james-dire-1/arduino-radio-project/R_images/IMG_2889.jpeg

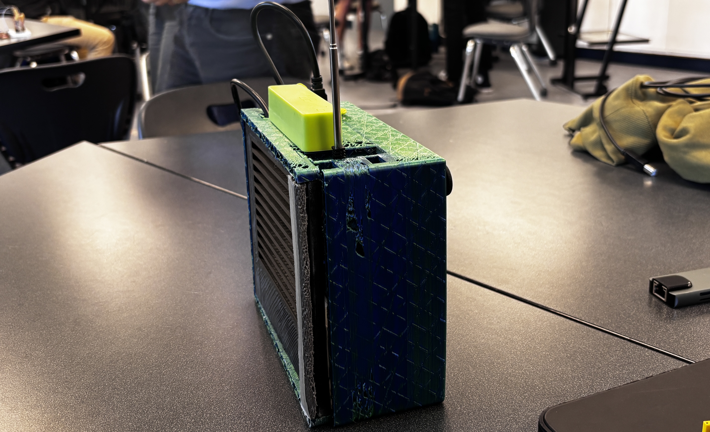
R_images/IMG_2889.jpeg
