james-dire-1/arduino-radio-project/R_images/IMG_2890.jpeg

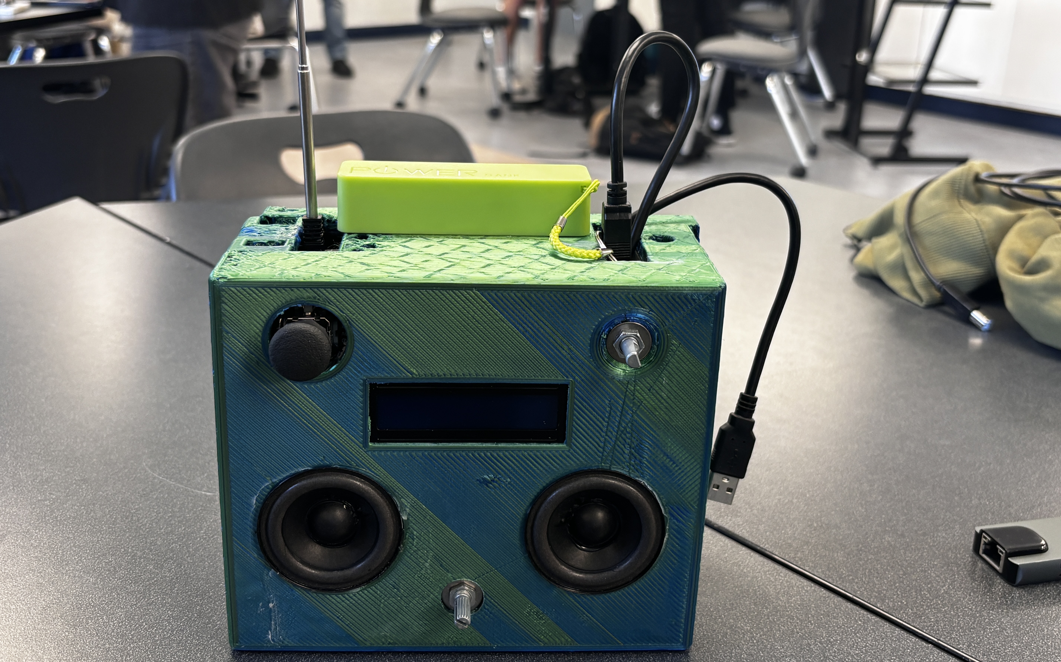
R_images/IMG_2890.jpeg
