james-dire-1/arduino-radio-project/R_other/CircuitDiagramImages/Screenshot 2025-05-31 at 1.21.56 PM.png

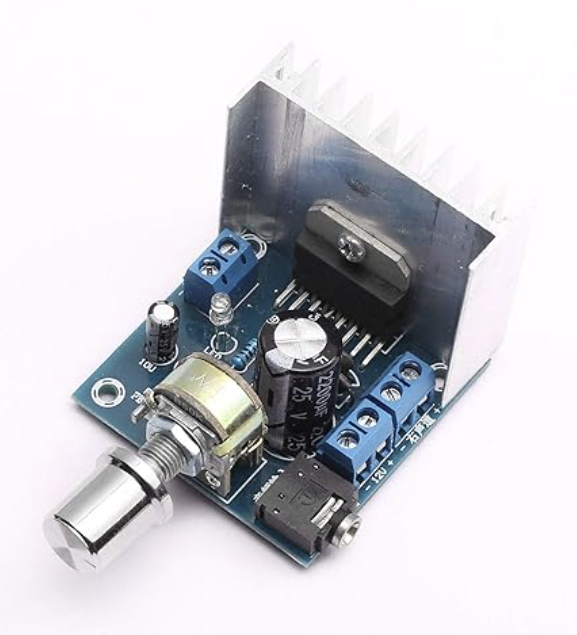
R_other/CircuitDiagramImages/Screenshot 2025-05-31 at 1.21.56 PM.png
