james-dire-1/arduino-radio-project/R_other/CircuitDiagramImages/TEA5767_fm_radio_module.webp

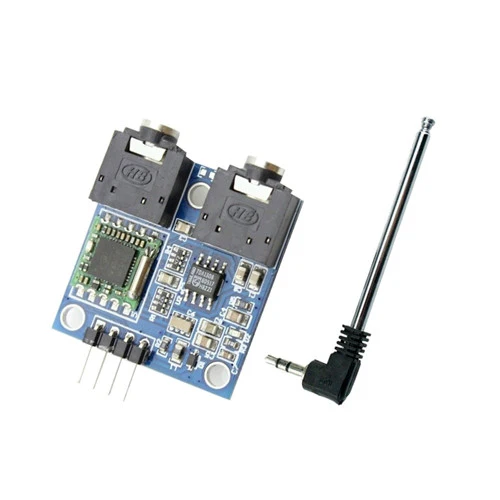
R_other/CircuitDiagramImages/TEA5767_fm_radio_module.webp
