james-dire-1/arduino-radio-project/R_other/SlideshowImages/6c5313c7-2e61-486a-ad82-d5e051c6e02a.png

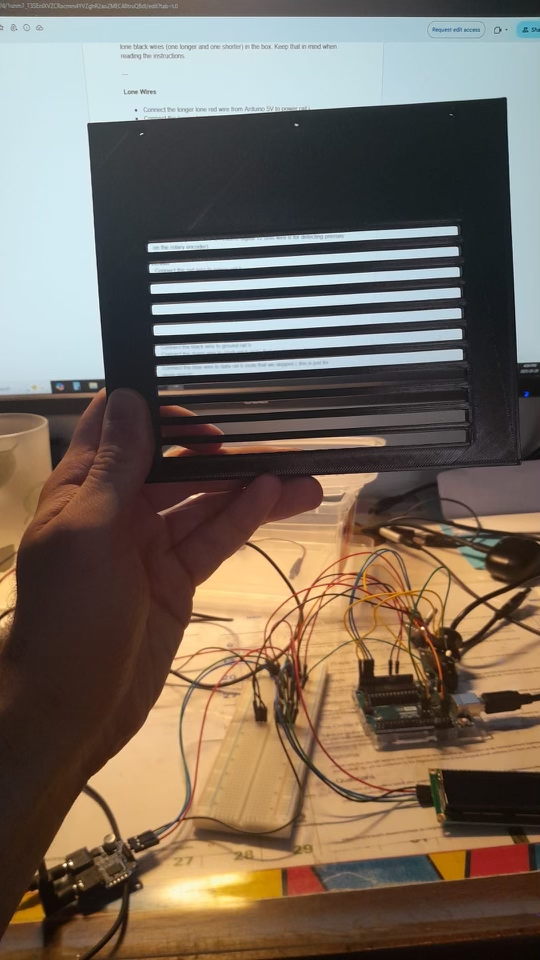
R_other/SlideshowImages/6c5313c7-2e61-486a-ad82-d5e051c6e02a.png
