james-dire-1/arduino-radio-project/R_other/SlideshowImages/7ecfe39c-ecb8-46d4-9817-e5481a1effc0.png

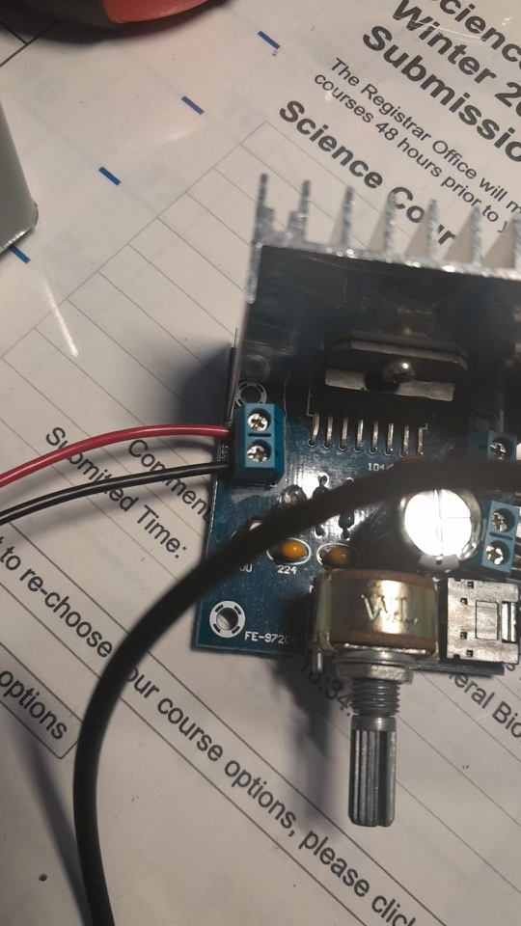
R_other/SlideshowImages/7ecfe39c-ecb8-46d4-9817-e5481a1effc0.png
