james-dire-1/arduino-radio-project/R_other/SlideshowImages/62ca493e-6e24-47a5-971f-845fc1b9c889.png

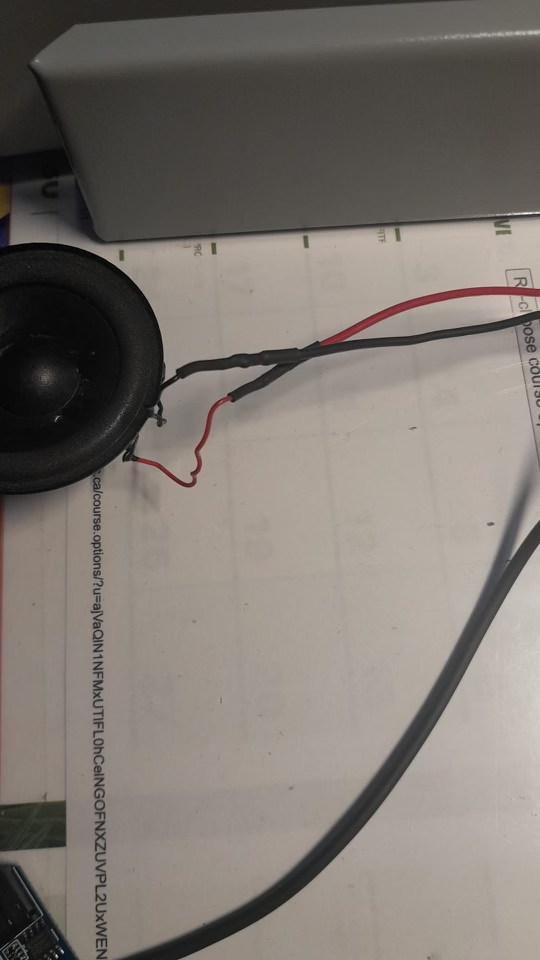
R_other/SlideshowImages/62ca493e-6e24-47a5-971f-845fc1b9c889.png
