james-dire-1/arduino-radio-project/R_other/SlideshowImages/95d62d8a-2fb8-4f7a-9237-26453b7603f2.png

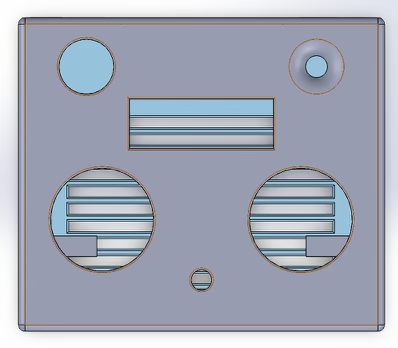
R_other/SlideshowImages/95d62d8a-2fb8-4f7a-9237-26453b7603f2.png
