james-dire-1/arduino-radio-project/R_other/SlideshowImages/ca7dd065-f66f-4d62-96de-7c329f59c99d.png

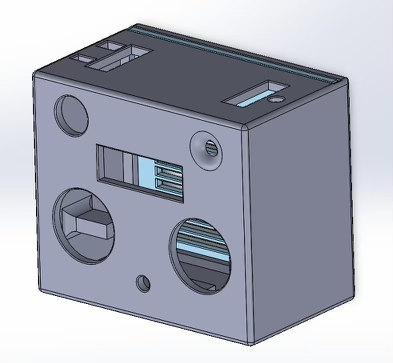
R_other/SlideshowImages/ca7dd065-f66f-4d62-96de-7c329f59c99d.png
