james-dire-1/arduino-radio-project/R_other/SlideshowImages/cb82eedb-ceaf-4a4e-8e40-77120ef748f7.png

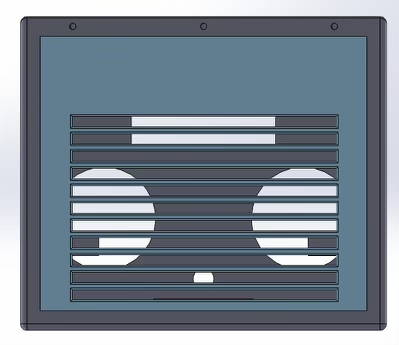
R_other/SlideshowImages/cb82eedb-ceaf-4a4e-8e40-77120ef748f7.png
