james-dire-1/arduino-radio-project/R_other/SlideshowImages/e50d46db-6967-4ef9-a702-23a1209742e0.png

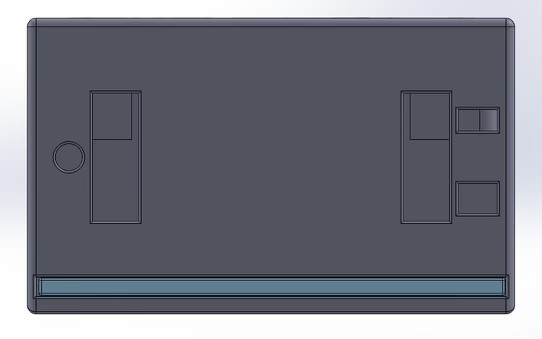
R_other/SlideshowImages/e50d46db-6967-4ef9-a702-23a1209742e0.png
