james-dire-1/arduino-radio-project/R_other/SlideshowImages/IMG_7158.jpeg

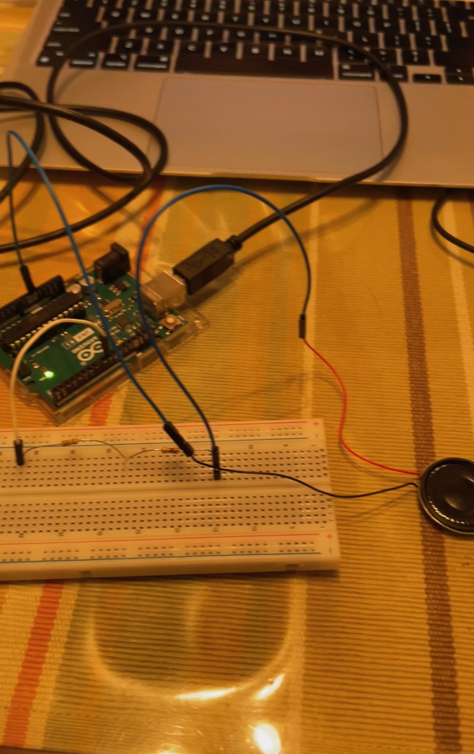
R_other/SlideshowImages/IMG_7158.jpeg
