james-dire-1/arduino-radio-project/R_other/SlideshowImages/Screenshot 2025-05-29 at 11.53.12 PM.png

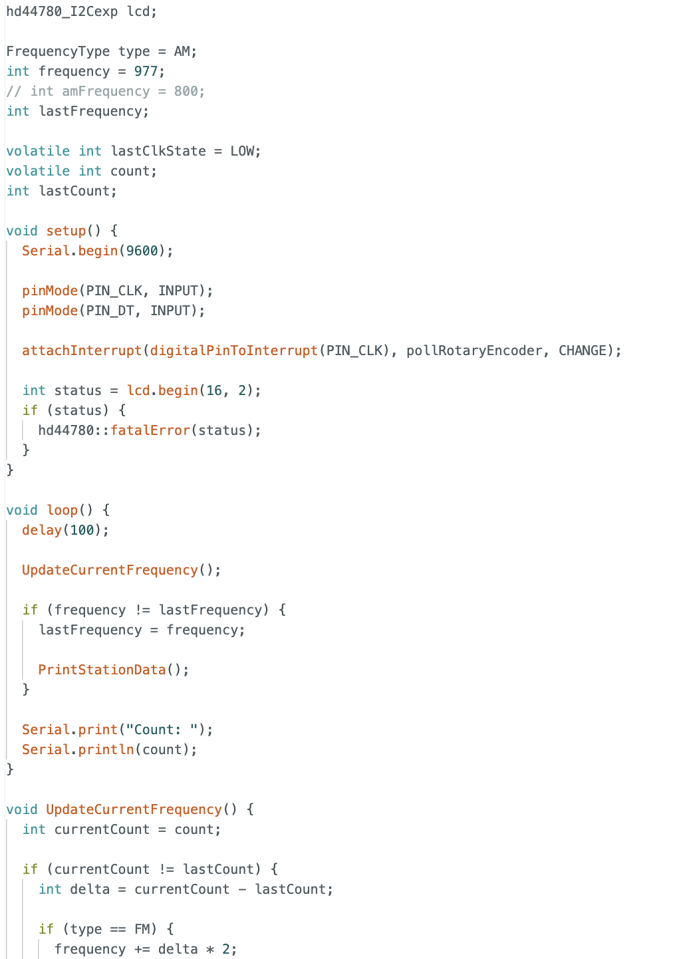
R_other/SlideshowImages/Screenshot 2025-05-29 at 11.53.12 PM.png
