james-dire-1/arduino-radio-project/R_other/SlideshowImages/Screenshot 2025-05-30 at 10.29.55 AM.png

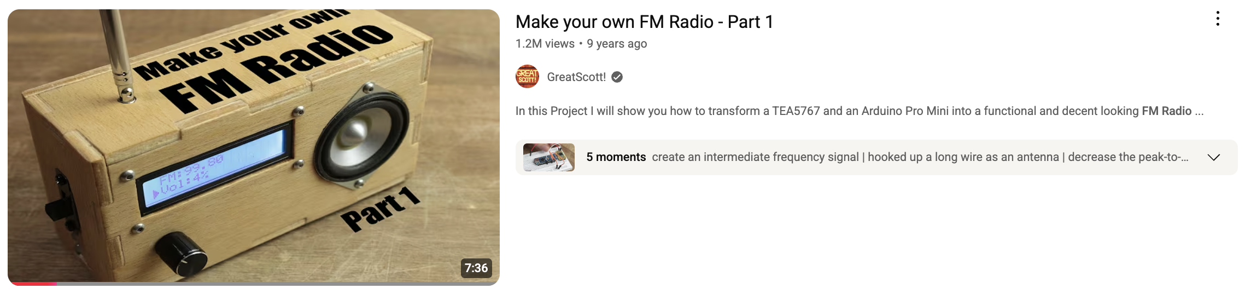
R_other/SlideshowImages/Screenshot 2025-05-30 at 10.29.55 AM.png
