james-dire-1/arduino-radio-project/R_other/SlideshowImages/Screenshot 2025-05-30 at 12.46.17 AM.png

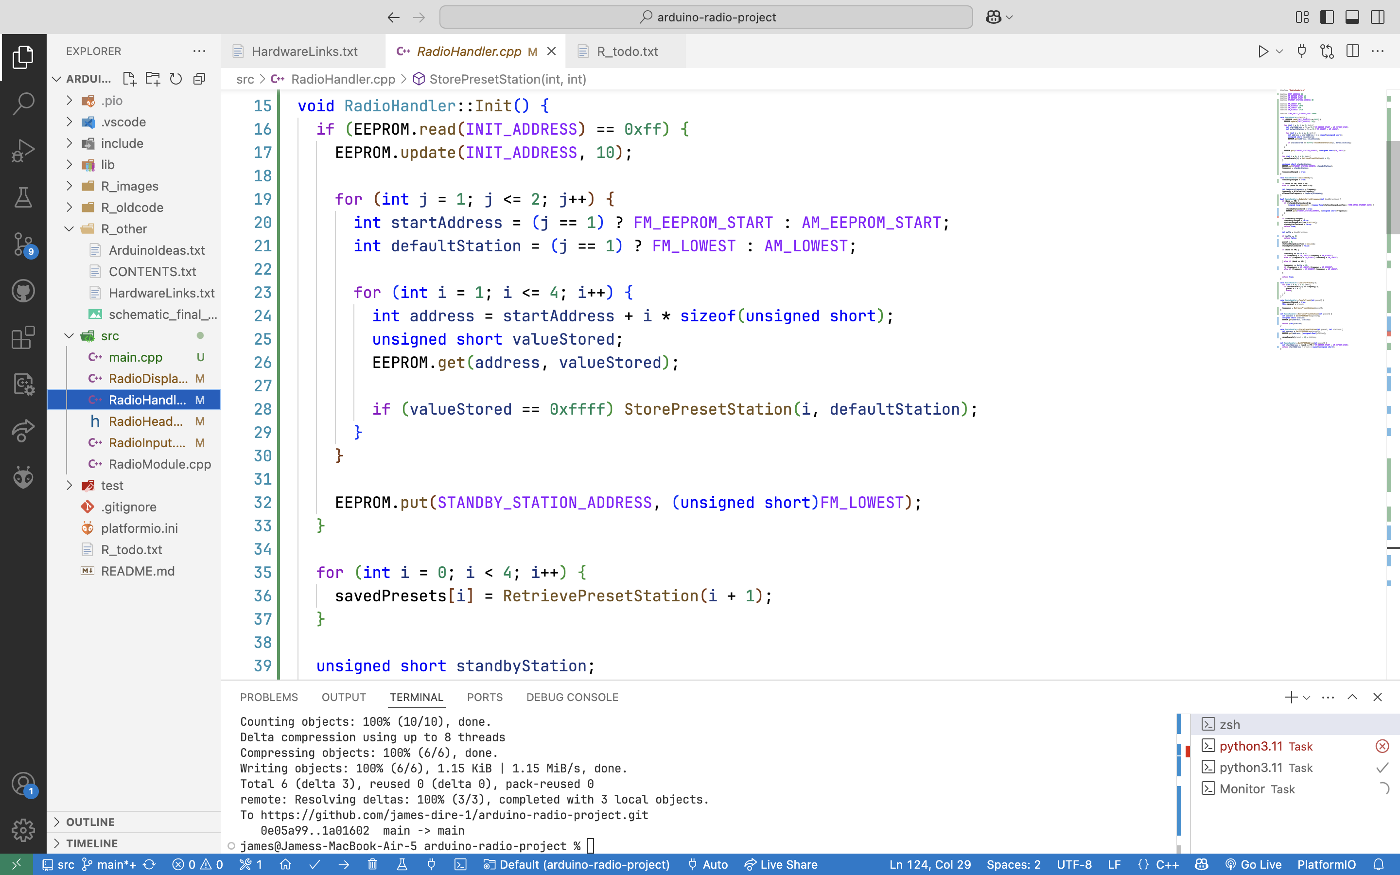
R_other/SlideshowImages/Screenshot 2025-05-30 at 12.46.17 AM.png
